OLIMEX/RVPC/SOFTWARE/Demo-VGA/src/chardefs.h

// File: chardefs.h
// Purpose: Character glyph definitions
//
// This file uses a series of macros so that it can group the pixel bits of
// each character together, visually, in this source file, while still being
// able to group scan lines together, physically, in flash memory. In this
// source file, each character glyph is shown as a series of 8 macros,
// representing scan lines #0..#7 of that specific character. In the
// compiled binary, the "character_defs" array is arranged by scan line
// first, then by character index, so all of the scan line #0 bytes are
// together (for characters #00..#FF), followed by all of the scan line
// #1 bytes (for characters #00..#FF), and so on.
//

#ifndef __CHARDEFS_H
#define __CHARDEFS_H

#include <stdint.h>

#define CHARS_COUNT 128

#if     CHARS_COUNT > 128
#define CHARS_COUNT_MASK 0b11111111
#elif   CHARS_COUNT > 64
#define CHARS_COUNT_MASK 0b01111111
#elif   CHARS_COUNT > 32
#define CHARS_COUNT_MASK 0b00111111
#elif   CHARS_COUNT > 16
#define CHARS_COUNT_MASK 0b00011111
#else
#define CHARS_COUNT_MASK 0b00001111
#endif

#define CHAR_WIDTH       8

#define CHAR_HEIGHT      8
#define CHAR_HEIGHT_BITS 0x03
#define CHAR_HEIGHT_MASK 0b00000111

#define SPLIT_VALUE(val) \
            ((((val>>7)&1)?(1<<2):(1<<18)) | \
             (((val>>6)&1)?(1<<3):(1<<19)) | \
             (((val>>5)&1)?(1<<4):(1<<20)) | \
             (((val>>4)&1)?(1<<5):(1<<21)) | \
             (((val>>3)&1)?(1<<6):(1<<22)) | \
             (((val>>2)&1)?(1<<7):(1<<23)) | \
             (((val>>1)&1)?(1<<8):(1<<24)) | \
             (((val>>0)&1)?(1<<9):(1<<25)))

//--------------------------------

#define CHAR_DEF_0x00_0 0b00000000
#define CHAR_DEF_0x00_1 0b00000000
#define CHAR_DEF_0x00_2 0b00000000
#define CHAR_DEF_0x00_3 0b00000000
#define CHAR_DEF_0x00_4 0b00000000
#define CHAR_DEF_0x00_5 0b00000000
#define CHAR_DEF_0x00_6 0b00000000
#define CHAR_DEF_0x00_7 0b00000000

#define CHAR_DEF_0x01_0 0b11111111
#define CHAR_DEF_0x01_1 0b00000000
#define CHAR_DEF_0x01_2 0b00000000
#define CHAR_DEF_0x01_3 0b00000000
#define CHAR_DEF_0x01_4 0b00000000
#define CHAR_DEF_0x01_5 0b00000000
#define CHAR_DEF_0x01_6 0b00000000
#define CHAR_DEF_0x01_7 0b00000000

#define CHAR_DEF_0x02_0 0b00000000
#define CHAR_DEF_0x02_1 0b00000000
#define CHAR_DEF_0x02_2 0b00000000
#define CHAR_DEF_0x02_3 0b00000000
#define CHAR_DEF_0x02_4 0b00000000
#define CHAR_DEF_0x02_5 0b00000000
#define CHAR_DEF_0x02_6 0b00000000
#define CHAR_DEF_0x02_7 0b11111111

#define CHAR_DEF_0x03_0 0b11111111
#define CHAR_DEF_0x03_1 0b10000000
#define CHAR_DEF_0x03_2 0b10000000
#define CHAR_DEF_0x03_3 0b10000000
#define CHAR_DEF_0x03_4 0b10000000
#define CHAR_DEF_0x03_5 0b10000000
#define CHAR_DEF_0x03_6 0b10000000
#define CHAR_DEF_0x03_7 0b10000000

#define CHAR_DEF_0x04_0 0b11111111
#define CHAR_DEF_0x04_1 0b00000001
#define CHAR_DEF_0x04_2 0b00000001
#define CHAR_DEF_0x04_3 0b00000001
#define CHAR_DEF_0x04_4 0b00000001
#define CHAR_DEF_0x04_5 0b00000001
#define CHAR_DEF_0x04_6 0b00000001
#define CHAR_DEF_0x04_7 0b00000001

#define CHAR_DEF_0x05_0 0b10000000
#define CHAR_DEF_0x05_1 0b10000000
#define CHAR_DEF_0x05_2 0b10000000
#define CHAR_DEF_0x05_3 0b10000000
#define CHAR_DEF_0x05_4 0b10000000
#define CHAR_DEF_0x05_5 0b10000000
#define CHAR_DEF_0x05_6 0b10000000
#define CHAR_DEF_0x05_7 0b11111111

#define CHAR_DEF_0x06_0 0b00000001
#define CHAR_DEF_0x06_1 0b00000001
#define CHAR_DEF_0x06_2 0b00000001
#define CHAR_DEF_0x06_3 0b00000001
#define CHAR_DEF_0x06_4 0b00000001
#define CHAR_DEF_0x06_5 0b00000001
#define CHAR_DEF_0x06_6 0b00000001
#define CHAR_DEF_0x06_7 0b11111111

#define CHAR_DEF_0x07_0 0b10000000
#define CHAR_DEF_0x07_1 0b10000000
#define CHAR_DEF_0x07_2 0b10000000
#define CHAR_DEF_0x07_3 0b10000000
#define CHAR_DEF_0x07_4 0b10000000
#define CHAR_DEF_0x07_5 0b10000000
#define CHAR_DEF_0x07_6 0b10000000
#define CHAR_DEF_0x07_7 0b10000000

#define CHAR_DEF_0x08_0 0b00000001
#define CHAR_DEF_0x08_1 0b00000001
#define CHAR_DEF_0x08_2 0b00000001
#define CHAR_DEF_0x08_3 0b00000001
#define CHAR_DEF_0x08_4 0b00000001
#define CHAR_DEF_0x08_5 0b00000001
#define CHAR_DEF_0x08_6 0b00000001
#define CHAR_DEF_0x08_7 0b00000001

#define CHAR_DEF_0x09_0 0b00000000
#define CHAR_DEF_0x09_1 0b00000000
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
        CHAR_LINE(n, 0xD8), \
        CHAR_LINE(n, 0xD9), \
        CHAR_LINE(n, 0xDA), \
        CHAR_LINE(n, 0xDB), \
        CHAR_LINE(n, 0xDC), \
        CHAR_LINE(n, 0xDD), \
        CHAR_LINE(n, 0xDE), \
        CHAR_LINE(n, 0xDF), \
        \
        CHAR_LINE(n, 0xE0), \
        CHAR_LINE(n, 0xE1), \
        CHAR_LINE(n, 0xE2), \
        CHAR_LINE(n, 0xE3), \
        CHAR_LINE(n, 0xE4), \
        CHAR_LINE(n, 0xE5), \
        CHAR_LINE(n, 0xE6), \
        CHAR_LINE(n, 0xE7), \
        CHAR_LINE(n, 0xE8), \
        CHAR_LINE(n, 0xE9), \
        CHAR_LINE(n, 0xEA), \
        CHAR_LINE(n, 0xEB), \
        CHAR_LINE(n, 0xEC), \
        CHAR_LINE(n, 0xED), \
        CHAR_LINE(n, 0xEE), \
        CHAR_LINE(n, 0xEF), \
        \
        CHAR_LINE(n, 0xF0), \
        CHAR_LINE(n, 0xF1), \
        CHAR_LINE(n, 0xF2), \
        CHAR_LINE(n, 0xF3), \
        CHAR_LINE(n, 0xF4), \
        CHAR_LINE(n, 0xF5), \
        CHAR_LINE(n, 0xF6), \
        CHAR_LINE(n, 0xF7), \
        CHAR_LINE(n, 0xF8), \
        CHAR_LINE(n, 0xF9), \
        CHAR_LINE(n, 0xFA), \
        CHAR_LINE(n, 0xFB), \
        CHAR_LINE(n, 0xFC), \
        CHAR_LINE(n, 0xFD), \
        CHAR_LINE(n, 0xFE), \
        CHAR_LINE(n, 0xFF)

#if   CHARS_COUNT > 128
#define CHARSET_LINE(n) \
    { \
        CHARSET_LINE_4b(n), \
        CHARSET_LINE_5b(n), \
        CHARSET_LINE_6b(n), \
        CHARSET_LINE_7b(n), \
        CHARSET_LINE_8b(n)  \
    }
#elif CHARS_COUNT > 64
#define CHARSET_LINE(n) \
    { \
        CHARSET_LINE_4b(n), \
        CHARSET_LINE_5b(n), \
        CHARSET_LINE_6b(n), \
        CHARSET_LINE_7b(n)  \
    }
#elif CHARS_COUNT > 32
#define CHARSET_LINE(n) \
    { \
        CHARSET_LINE_4b(n), \
        CHARSET_LINE_5b(n), \
        CHARSET_LINE_6b(n)  \
    }
#elif CHARS_COUNT > 16
    { \
        CHARSET_LINE_4b(n), \
        CHARSET_LINE_5b(n)  \
    }
#else
#define CHARSET_LINE(n) \
    { \
        CHARSET_LINE_4b(n) \
    }
#endif

#endif // CHARDEFS_H
